evanbrumley/arkham-card-boxes/images/img1.jpg

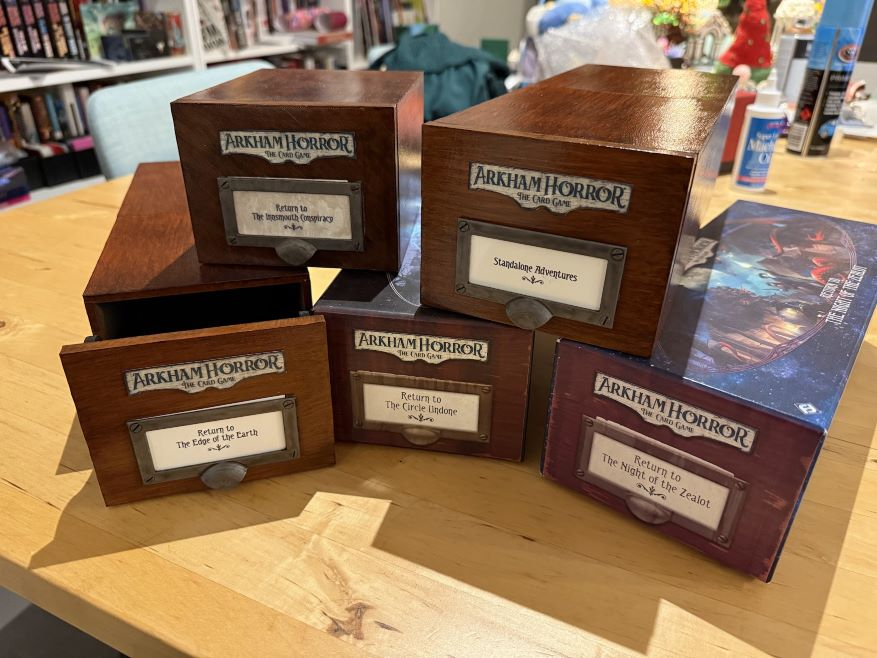
images/img1.jpg
