evanbrumley/arkham-card-boxes/images/img2.jpg

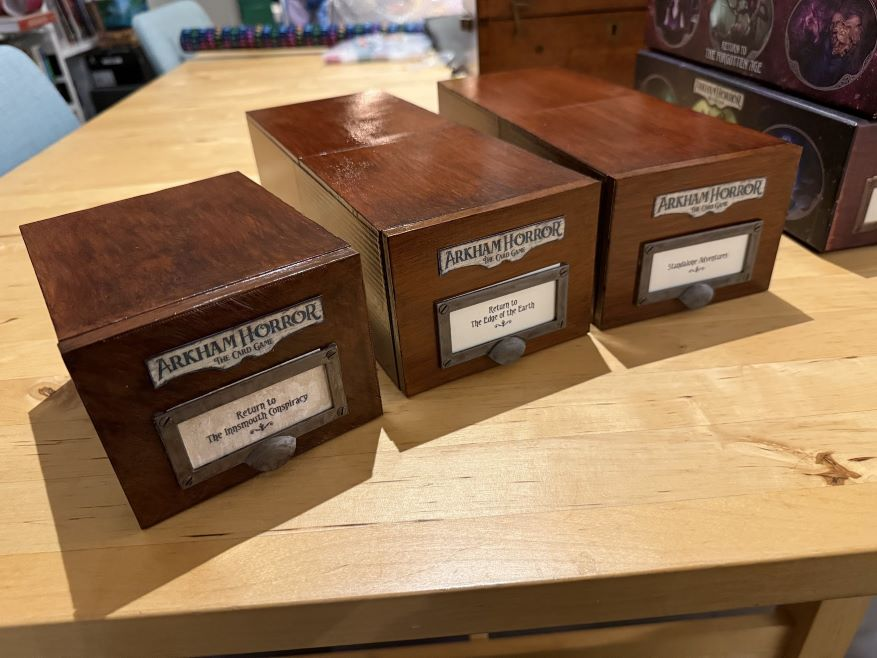
images/img2.jpg
