evanbrumley/arkham-card-boxes/images/img3.jpg

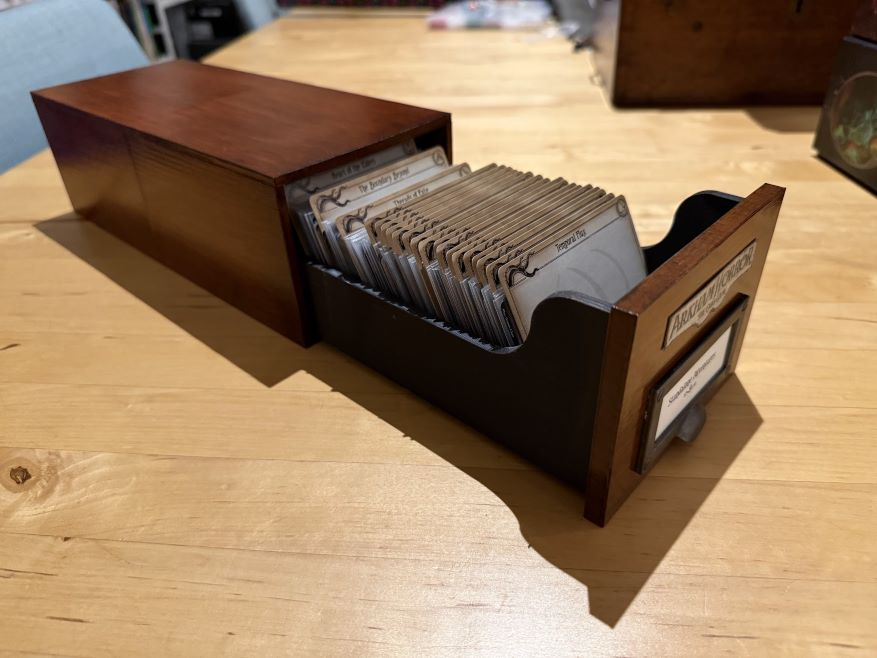
images/img3.jpg
