evanbrumley/arkham-card-boxes/images/img4.jpg

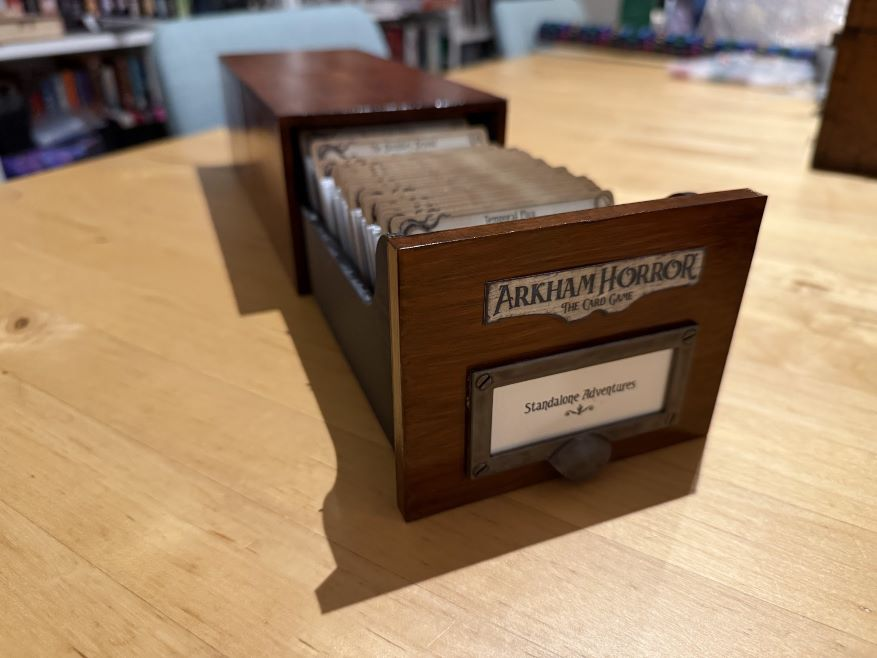
images/img4.jpg
