evanbrumley/arkham-card-boxes/296mm_split/Drawer Rear.stl

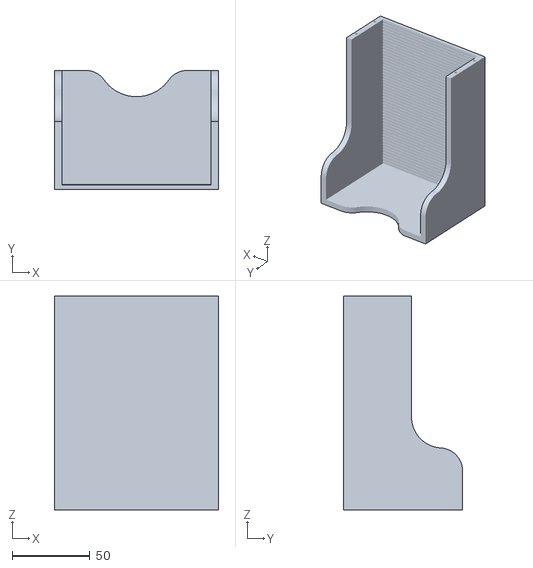
[picture p19: CAD file, 2024-11-09]
296mm_split/Drawer Rear.stl
106.0 x 77.0 x 138.0
