evanbrumley/arkham-card-boxes/170mm/Shell.stl

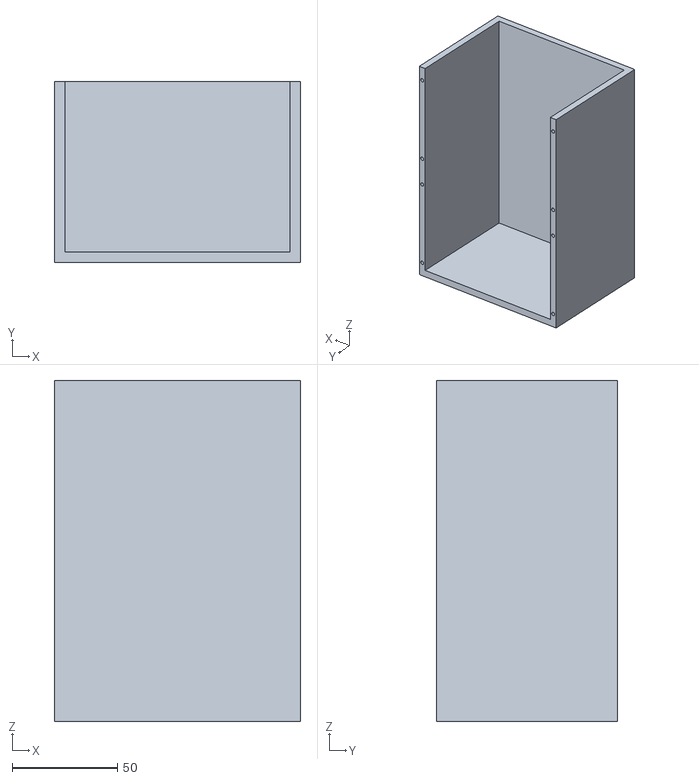
[picture p20: CAD file, 2024-11-09]
170mm/Shell.stl
117.0 x 86.0 x 162.0
