evanbrumley/arkham-card-boxes/200mm/Shell.stl

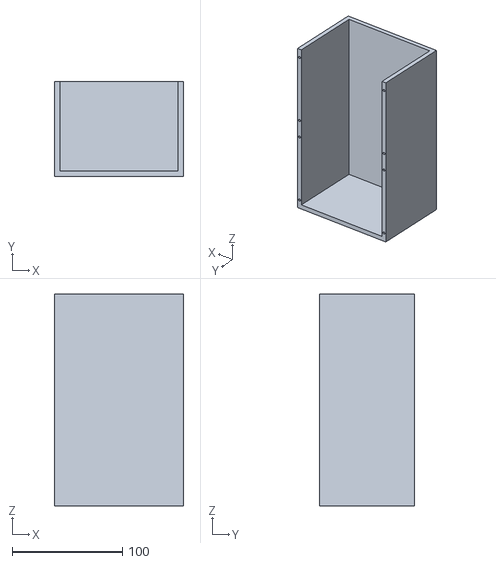
[picture p21: CAD file, 2024-11-09]
200mm/Shell.stl
117.0 x 86.0 x 192.0
