evanbrumley/arkham-card-boxes/240mm/Shell.stl

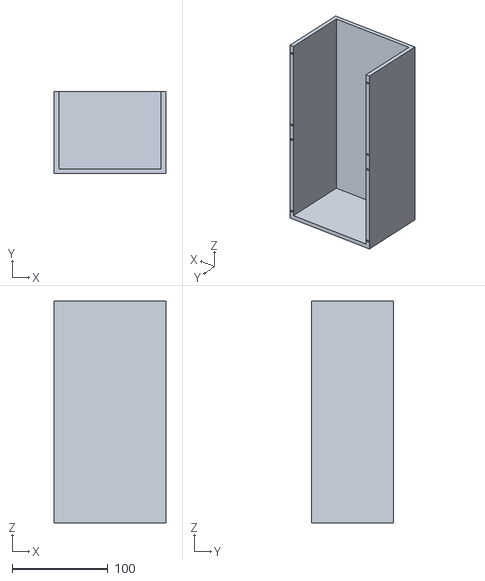
[picture p22: CAD file, 2024-11-09]
240mm/Shell.stl
117.0 x 86.0 x 232.0
