evanbrumley/arkham-card-boxes/296mm/Drawer.stl

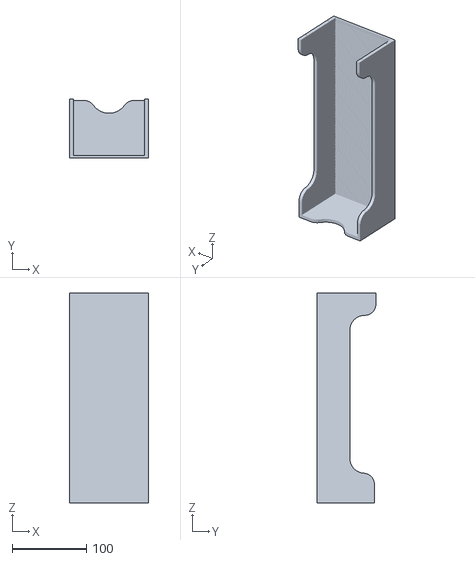
[picture p23: CAD file, 2024-11-09]
296mm/Drawer.stl
106.0 x 79.0 x 282.0
