evanbrumley/arkham-card-boxes/296mm_split/Pin.stl

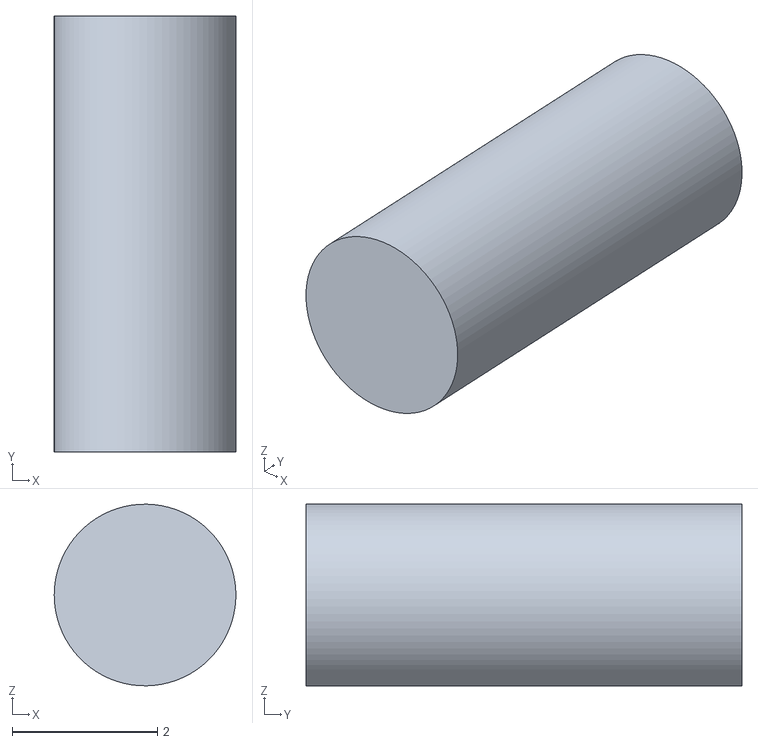
[picture p24: CAD file, 2024-11-09]
296mm_split/Pin.stl
2.50 x 6.00 x 2.50
