evanbrumley/arkham-card-boxes/296mm_split/Drawer Front.stl

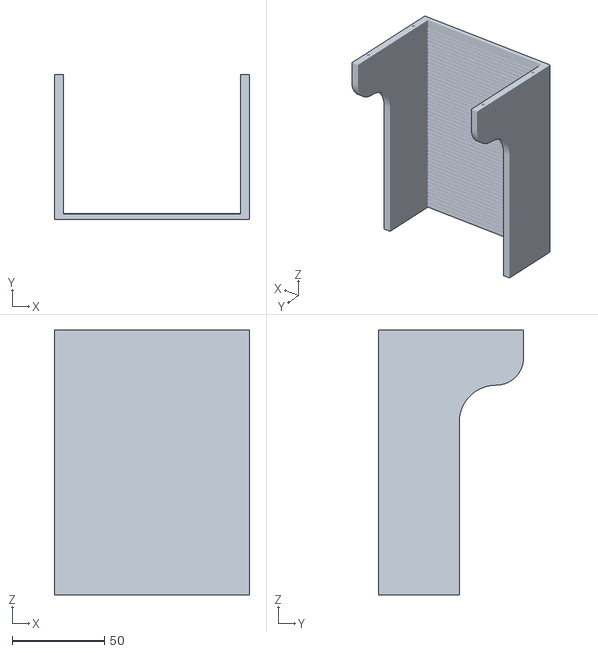
[picture p25: CAD file, 2024-11-09]
296mm_split/Drawer Front.stl
106.0 x 79.0 x 144.0
